typoena/typewriter/docs/adr.md

# Architecture Decision Records

A running log of the load-bearing technical decisions on this project.
Each record states what was considered, what we chose, and what we accept
as a consequence. Status moves from **Proposed** → **Accepted** →
(eventually) **Superseded** when a later ADR replaces it.

Format inspired by Michael Nygard's ADR template, kept short on purpose.

**Related docs:** [`../CONTEXT.md`](../CONTEXT.md) — the glossary and the
principles that constrain [ADR-010]. [`qfd.md`](quality/qfd.md) — the tradeoffs
below, ranked by user-facing weight. [`macroplan.md`](plan/macroplan.md) —
per-version scope.

---

## ADR-001: Language and runtime — Rust on `esp-idf-rs` (std)

**Status:** Accepted — 2026-05-14
**Scope:** Whole project.

### Context

The firmware needs: USB host, Wi-Fi + TLS, SPI peripherals, a SD filesystem,
and a working git implementation that can push over HTTPS. All on an ESP32-S3
with 8 MB PSRAM. We also want the code to stay refactorable as features pile
up across nine downstream releases.

### Options considered

| Option | Pros | Cons |
| --- | --- | --- |
| **C on ESP-IDF (no Arduino)** | Reference platform on the bare native SDK; every peripheral has a driver; smallest binary of the C-family options; no C++ runtime / exceptions / RTTI to reason about. | All memory safety on you; no RAII for resource cleanup; no generics so widget / state code gets repetitive; refactoring at scale is painful. |
| **C++ on ESP-IDF** | Same peripheral coverage as C; RAII, templates, and `std::` containers ease widget / state code; mature in the ESP-IDF examples. | Exception / RTTI story on embedded is messy; ABI / linker surprises; memory safety still on you; binary larger than plain C. |
| **Rust on `esp-idf-rs` (std)**  | First-class Espressif-sponsored Rust support; `std` gives heap / threads / VFS / mbedtls; can use the broader Rust ecosystem (`gitoxide`, `ropey`, `embedded-graphics`). | Larger binary than `no_std`; longer build times; some `unsafe` at FFI seams. |
| **Rust on `esp-hal` (no_std)**  | Smallest binary, most "pure" embedded experience. | No `std` = no off-the-shelf git, no easy TLS, would re-implement a lot of plumbing. |
| **Gleam + Shore on AtomVM** | Beautiful language, the user's stated preference. | BEAM on ESP32 is memory-hungry; no bindings for USB host, e-ink, SD, TLS, git in that ecosystem. Two research projects stacked. |
| **MicroPython / CircuitPython** | Fastest to prototype. | Too slow for responsive editing at the latencies e-ink already imposes; GC pauses would surface as dropped keys. |
| **TinyGo** | Modern, ergonomic. | ESP32-S3 support is thinner than Rust's; smaller ecosystem of embedded crates equivalents. |

### Decision

**Rust on `esp-idf-rs` (std).** It's the sweet spot: keeps the door open to
the entire Rust ecosystem we need (`gitoxide` especially), gets us threads
and TLS without writing them, and has Espressif as an actual upstream.

### Consequences

- Binary will be in the 1–2 MB range — comfortable in 16 MB flash.
- Build times are real (clean build ~5–10 min). Acceptable.
- Cross-compiling toolchain (`espup`) is one more thing to install.
- We will not use `tokio` or async runtimes in v0.1 — see [ADR-006].
- Revisit if `esp-idf-rs` upstream stalls or if `gitoxide` doesn't compile
  cleanly against it (spike 7 was the kill-switch — see [ADR-004]'s Outcome).

See also: [qfd-tradeoffs.md §7](quality/qfd.md#7-tradeoffs-and-their-why-linked-to-adrs) for
the binary-size / build-time costs traded against ecosystem access.

---

## ADR-002: UI strategy — custom widgets on `embedded-graphics`, not Ratatui

**Status:** Accepted — 2026-05-14
**Scope:** Whole project.

### Context

We need a TUI-like editor (header, edit area, status, palettes later). The
output medium is e-ink: pixel framebuffer with **partial-refresh windows**
aligned to panel-internal regions, ~10× slower than an LCD per region.

### Options considered

| Option | Pros | Cons |
| --- | --- | --- |
| **Ratatui** with a custom backend | Mature widget set, well-known API, lots of community examples. | Built for char-grid terminals over ANSI; per-cell diff fights e-ink's region-refresh model; backend would re-rasterise glyphs from cell-diffs; ~200 KB of binary and a leaky abstraction. |
| **Raw `embedded-graphics` only** | Smallest footprint, full control. | Every screen built from primitives; no widget reuse; status line / palette would each be ad-hoc. |
| **LVGL via Rust bindings** | Full GUI toolkit, themable. | Designed for actively-refreshing colour LCDs; e-ink integration is awkward; way more than we need. |
| **Custom thin widget layer on `embedded-graphics`** | Borrow Ratatui's API ideas (`Layout`, `Block`, `Paragraph`) without its rendering model; dirty-rect tracking aligned to e-ink regions; ~500 LoC. | We own and maintain the layer. |

### Decision

**Custom thin widget layer on `embedded-graphics`.** Steal the widget _API
shape_ from Ratatui (because it's a good shape) but render directly to a
pixel framebuffer with our own dirty-rectangle tracking sized to the panel's
refresh regions.

### Consequences

- ~500 LoC of widget/layout code we maintain. Worth it.
- We can tune refresh cadence (partial vs full) at the widget level.
- If we later want to render to a terminal for desktop testing, we add a
  second backend; the widget API stays.

Implementation: the `app::render` engine ([stack](reference/stack.md)).
Owns the two top-ranked functions (H1 latency, H2 region area) in
[qfd-house-1.md §3](quality/qfd-house-1.md#3-house-of-quality--whats--hows).

---

## ADR-003: Display medium — e-ink (GDEY0579T93 panel)

**Status:** Accepted — 2026-05-14
**Scope:** v0.1 through v1.0. 10.3" e-ink upgrade remains on the v1.x table; a non-e-ink swap would supersede this ADR.

### Context

The display has the largest downstream blast radius of any hardware choice.
The _medium_ (e-ink vs. LCD vs. memory LCD vs. OLED) — not the specific
panel — is the real architectural decision: it sets the render strategy
([ADR-002]), the per-keystroke latency floor, the idle-power profile (and
so the v0.8 battery story — [ADR-008]), the UX posture, and the BOM shape.
The specific panel (GDEY0579T93 + DESPI-c579 breakout) is already on hand
and documented here as the _instantiation_, not as a freshly weighed option.

This ADR records the medium choice with eyes open. E-ink has well-known
costs at the typing latencies a writing appliance wants — Astrohaus shipped
the Freewrite Alpha in 2023 on a reflective LCD specifically to address
typing-latency complaints from their original e-ink line. We are accepting
costs the category leader retreated from.

### Options considered

| Option | Refresh / persistence | Pros | Cons |
| --- | --- | --- | --- |
| **E-ink (reflective, image-persistent)** | ~100–300 ms partial / ~700–1000 ms full / persists at 0 W | Paper aesthetic; persists at zero idle power; no backlight (no glare, no eye strain); category convention (Freewrite, reMarkable, Kindle Scribe, Boox); medium enforces writing posture | Slow per-keystroke feedback; ghosting accumulates → periodic full-refresh flash; scroll is the worst-case refresh op (full edit-area redraw); requires waveform / refresh-cadence tuning; Astrohaus retreated from e-ink in Freewrite Alpha (2023) on typing-latency grounds |
| **FSTN graphical LCD (monochrome)** | <16 ms, no refresh quirks | Cheap (~$5–15); trivial render code; snappy scroll | Backlit (always-on power), unreadable indoors without it; no image persistence; calculator / feature-phone aesthetic; writing-grade resolution (≥600 px wide at ≥6") effectively unavailable as a hobbyist part |
| **Sharp Memory LCD (monochrome, reflective)** | ~20 ms, persists at near-0 W | Persists _and_ refreshes fast (best technical combo); sun-readable; ghost-free | Caps around 4.4" before getting rare and expensive; reflective-only feels like a screen, not paper; niche sourcing; lower DPI than e-ink at writing size |
| **TFT / OLED (color, self-lit or backlit)** | <16 ms, persists only at full power | Bright, fast, plentiful | Backlit / self-lit → screen-feel, not paper; OLED burns in static text (status line, header); defeats the writing-tool posture; not seriously a contender |

### Decision

**E-ink as the display medium**, instantiated with the **GDEY0579T93 (5.79",
792×272, SSD1683-class) driven over SPI through the DESPI-c579 breakout** —
which is already on hand. The DESPI-c579 is a passive level-shifter / FPC
adapter, not an active controller — same SPI driver model as any other
e-paper.

The medium is chosen for: paper aesthetic, zero-idle-power persistence
(which makes [ADR-008]'s battery deferral structurally cheap to revisit at
v0.8), the category convention users have a mental model for, and alignment
with the "writing tool, not screen" posture pinned in
[`CONTEXT.md`](../CONTEXT.md). The slow refresh and scroll cost are accepted
as the price of those properties.

### Consequences

- Visible writing column on this panel is ~13 lines. UI must embrace the
  constraint — no multi-pane, no large headers. Region vocabulary:
  [`CONTEXT.md` → screen regions](../CONTEXT.md#screen-regions).
- Framebuffer is ~27 KB; keeps PSRAM free for git pack data — a top-3
  budget item in [qfd-budget.md §6](quality/qfd.md#6-critical-performance-budget).
- Driver: SSD1683-class. If `epd-waveshare` doesn't already cover this
  panel's controller, ~300 LoC of `embedded-hal` SPI driver. Validated in
  [spike 2](../firmware/docs/bring-up-spikes.md).
- **Per-keystroke latency floor ~100–300 ms** (partial refresh). The render
  module must buffer the active line and flush on a short timer, not redraw
  on every keystroke. Owns the top-ranked H1 latency constraint in
  [qfd-house-1.md §3](quality/qfd-house-1.md#3-house-of-quality--whats--hows); strategy lives in
  [ADR-002].
- **Scroll is the worst-case refresh operation** — every scroll is a full
  edit-area redraw, either with a visible flash (full refresh) or
  accumulating ghost trails (partial refresh). The concrete scroll strategy is
  a render concern, not part of this ADR — the scope/trigger vocabulary is in
  [`CONTEXT.md` → refresh cycle](../CONTEXT.md#refresh-cycle).
- **Industry calibration:** Astrohaus shipped Freewrite Alpha (2023) on a
  reflective LCD specifically to fix typing-latency complaints from their
  e-ink line. The latency cost we're accepting is one the commercial leader
  couldn't fully tune away after a decade. Set expectations accordingly —
  do not promise "instant feedback."
- Idle power on e-ink is structurally ~0, which makes the battery sizing
  exercise straightforward — see [ADR-008] and
  [macroplan → v0.10](plan/macroplan.md#v010--power-battery--sleep---).
- 10.3" e-ink upgrade path is preserved by keeping the renderer
  resolution-agnostic. A _non_-e-ink swap (e.g. Sharp Memory LCD) would
  invalidate [ADR-002]'s dirty-rect strategy and force a fresh medium ADR.

---

## ADR-004: Git implementation — `gitoxide` (`gix`)

**Status:** Accepted — 2026-05-14
**Scope:** Whole project, all releases.

### Context

The device must do `add`, `commit`, `push` over the network. Optionally
later: `fetch`, `pull`, `branch`. The library must compile against
`esp-idf-rs` (std, mbedtls available).

### Options considered

| Option | Pros | Cons |
| --- | --- | --- |
| **`libgit2-sys`** (C bindings) | Battle-tested, comprehensive, well-known. | C dependency complicates cross-compile to ESP32-S3; needs mbedtls glue; binary size; less Rust-idiomatic. |
| **`gitoxide` (`gix`)** | Pure Rust, modular crates (we only depend on what we use), idiomatic API, active development. | Smart-HTTP push path is newer than libgit2's; PSRAM allocation patterns less battle-tested on embedded. |
| **Hand-rolled HTTP + pack** | Smallest possible footprint. | Reinventing git internals; pack delta + ref discovery + index updates are not weekend work. |
| **Shell out to `git` binary**  | Trivial. | There is no `git` binary on the ESP32-S3. |

### Decision

**`gitoxide`.** Modular means we pull only `gix-pack`, `gix-protocol`,
`gix-transport`, etc. — not 200 KB of features we don't use. Pure Rust
removes a class of cross-compile pain. The smart-HTTP path is validated in
spike 7 _before_ we commit to integration; if it fails on the device, we
fall back to `libgit2-sys` for v0.1 (documented as the kill-switch in the
risk table).

### Consequences

- We become an early-ish embedded user of `gitoxide`; bugs reported back
  upstream.
- Auth via PAT in an Authorization header — no SSH (see [ADR-005]).
- Performance on PSRAM during pack operations is a watched metric — top-3
  priority in [qfd-budget.md §6](quality/qfd.md#6-critical-performance-budget).

Implementation: the git row of [`stack.md`](reference/stack.md).

### Outcome — Spike 7, 2026-07-05: kill-switch fired

`gix` was ruled out for v0.1 and the fallback taken. gitoxide supports push only
over `file://` and `ssh://` — **not HTTP(S)** — so with HTTPS + PAT fixed by
[ADR-005], the smart-HTTP push path this ADR bet on does not exist yet. We
switched to **`libgit2` (`git2` crate)** and proved `add → commit → push`
(incl. `pull --no-edit` + retry) on desktop
([`spikes/spike7-git-push`](../spikes/spike7-git-push/README.md)). The remaining risk is
now the on-device **libgit2 → xtensa/mbedtls cross-compile** — the very pain
this ADR chose gix to avoid. Full context:
[postmortem](record/postmortems/2026-07-05-spike7-gix-https-push.md). Revisit gix if
its HTTP(S) push lands upstream before v0.1 ships.

---

## ADR-005: Auth — HTTPS + GitHub Personal Access Token

**Status:** Accepted — 2026-05-14
**Scope:** v0.1 through at least v0.9.

### Context

The device must authenticate to GitHub (or other git remotes) to push.
Auth has to be: enterable on a tiny screen-less first-run flow, storable
on-device, and reasonably secure for a personal appliance.

### Options considered

| Option | Pros | Cons |
| --- | --- | --- |
| **HTTPS + PAT** | Trivial to implement; PAT is a string the user pastes during captive-portal setup; works with `gitoxide` smart-HTTP. | Long-lived secret on device; PAT rotation is manual. |
| **HTTPS + OAuth device flow** | No secret typed by hand; user approves on github.com. | Adds an OAuth client app to maintain; token still has to live on device; more first-run UX work. |
| **SSH** | No PAT; per-device deploy keys. | SSH on embedded is heavy (host-key handling, key generation); `gitoxide`'s SSH transport story is less mature than HTTPS; users would have to register the public key on GitHub anyway. |
| **GitHub App with installation token** | Strongest model, rotating credentials. | Massive overhead for a single-user device. |

### Decision

**HTTPS + PAT.** In v0.1 the PAT (and all other config) is compiled into the
firmware binary via build-time env vars — the dev's-only-user model makes the
binary-as-secret-store acceptable. From v0.9 onward, the PAT moves to
encrypted LittleFS with a key derived from the chip's eFuse, so a stolen SD
card alone is not enough.

### Consequences

- The user (= dev, in v0.1) must generate a PAT with `repo` scope and supply
  it as a build-time env var. Provisioning is build-time only.
- PAT is never logged. Validated in code review.
- Rotation in v0.1 = wipe NVS and re-run setup. Proper rotation UI is v0.9
  — see [macroplan → v0.9](plan/macroplan.md#v09--robustness--).
- Revisit if we ever want to support multiple remotes per device with
  different credentials.

---

## ADR-006: Concurrency — `std::thread` + channels, no async runtime

**Status:** Accepted — 2026-05-14
**Scope:** v0.1 through at least v1.0.

### Context

The firmware has several concurrent concerns: USB input, Wi-Fi maintenance,
screen rendering, occasional git operations. None of them are I/O-bound at
the scale where async wins. The number of "tasks" is bounded and small (≤ 8).

### Options considered

| Option | Pros | Cons |
| --- | --- | --- |
| **`std::thread` + channels** | Boring, debuggable, stack traces work, no executor to tune; ESP-IDF FreeRTOS underneath is well-understood. | Each thread costs 8–32 KB stack depending on workload; not zero-cost like async. |
| **`embassy` async** | Trendy, ergonomic, low memory per task. | `esp-idf-rs` and `embassy` don't mix cleanly; adopting embassy means dropping `std` and rewriting against `esp-hal` ([ADR-001] reversed). |
| **`tokio` on `esp-idf-rs`** | Familiar async. | Heavy executor, oversized for ≤ 8 tasks, mbedtls/`gitoxide` integration would need a lot of glue. |
| **Single-threaded event loop** | Smallest memory. | Long-running ops (git push, full refresh) block input. |

### Decision

**`std::thread` + `crossbeam-channel`.** Five tasks (`usb`, `wifi`, `ui`,
`render`, `git`). Editor state behind a single `Mutex`. No `await`, no
runtime to tune, no colour-of-functions problem.

### Consequences

- Tens of KB of stack space across the task stacks — the measured sum and its
  ceiling are the H11 row of
  [qfd §6](quality/qfd.md#6-critical-performance-budget). Comfortable in the
  ESP32-S3's 512 KB internal SRAM.
- Refresh / git / Wi-Fi each get their own thread, so a slow push doesn't
  freeze typing.
- If task count balloons past ~10 (unlikely), revisit.

---

## ADR-007: Storage split — FAT-on-SD for working copy, LittleFS-on-flash for config

**Status:** Accepted — 2026-05-14
**Scope:** Whole project.

### Context

Two storage needs: a large, removable, growable area for the git working
copy and notes; and a small, durable, never-removed area for device config
(Wi-Fi credentials, PAT, remote URL).

### Options considered

| Option | Pros | Cons |
| --- | --- | --- |
| **SD (FAT) for working copy + LittleFS (internal) for config** | Plays to each medium's strengths; user can pop the SD to read on desktop; config can't be lost by yanking the card. | Two filesystems to manage. |
| **All on SD** | One filesystem. | Config disappears if SD is removed; PAT on FAT is harder to protect than on encrypted NVS. |
| **All in internal flash** | Single medium; encrypted. | 16 MB flash limits notes growth; no desktop-side access; SD slot becomes pointless. |
| **SPIFFS for everything** | Single FS, well-known on ESP32. | SPIFFS isn't great with large files; no removability. |

### Decision

**FAT on SD for `/sd/repo/` and `/sd/local/`. LittleFS on internal flash
for `/nvs/config.toml`.** PAT inside config is encrypted with an eFuse-
derived key.

### Consequences

- User can plug the SD into a laptop and read/edit files there.
  Discouraged but possible.
- Config survives SD reformatting.
- Power-loss safety on FAT is weaker than LittleFS — we mitigate with
  atomic-rename writes (`firmware::infrastructure::storage_sd`).
- **FatFS caveat (Spike 3, verified 2026-07-11):** FatFS's `f_rename` returns
  `FR_EXIST` on an existing destination — it does **not** replace like POSIX
  `rename(2)`. So the atomic save must `f_unlink` the target before renaming the
  `*.tmp` over it, and pair that with **boot recovery** of a lingering `*.tmp`.
  Recovery is _not_ simply "promote the tmp": a crash _during_ the tmp write
  leaves a partial tmp, so the choice depends on whether the target survived —
  - **tmp + target both present** → the crash could have been mid-write, so the
    tmp is untrustworthy. Keep the committed target, discard the tmp (this is the
    documented "you get the previous version" behaviour).
  - **tmp only, target absent** → the target was already unlinked, so the tmp is
    the newest complete, fsync'd copy and the only one left. Promote it.

  Implemented in `firmware::persistence::Storage::{save,recover}`. See the
  [Spike 3 postmortem](record/postmortems/2026-07-05-spike3-sd-cmd59.md#resolution-2026-07-11).

- **SD-card compatibility:** use a genuine card, ideally **≤32 GB (SDHC/FAT32)**.
  Large or counterfeit SDXC cards may reject `CMD59` (SPI-mode CRC) and fail to
  mount; we keep CRC required rather than run the user's writing over an
  unchecked bus. The device reports a swap-the-card message instead of a hex
  code.

### Outcome — the config half was never built

The working-copy half shipped as decided: FAT on SD at `/sd/repo` + `/sd/local`.
The config half did not. There is no LittleFS partition and no
`/nvs/config.toml`; device config lives in **`/sd/typoena.conf`**, plain text on
the same FAT card, written by either onboarding path (installer or wizard) and
read at boot through the `conf` crate. So config does _not_ survive a card
swap, and the eFuse-encrypted-at-rest endgame this ADR assumed is unbuilt —
tracked as the open [ADR-011]. A future ADR should supersede this one if the
split is ever revisited.

---

## ADR-008: MVP power — wall-powered, battery deferred to v0.8

**Status:** Accepted — 2026-05-14
**Scope:** v0.1 only. Revisited in ADR-future at v0.8.

### Context

"DIY typewriter" suggests portability, which suggests battery. But battery
adds: charging circuit, BMS, thermal margin, soft power switch, lid-close
detection, sleep states. Each of those has its own bring-up cost.

### Options considered

- **USB-C wall power, no battery.** Simple, safe, lets us measure real
  draw before sizing a cell.
- **18650 + IP5306 from day one.** Pretty close to a known-good pattern;
  IP5306 handles charge + 5 V boost.
- **LiPo + dedicated charger IC + buck/boost.** More control, more parts.

### Decision

**Wall power only for v0.1.** Battery is its own phase (v0.8) once the
power profile of "boot + type + idle + push" is measured on real hardware.
Sizing a battery before measuring is guessing.

### Consequences

- v0.1 device is tethered. Not the final aesthetic, but the right MVP.
- We can decide cell capacity from real numbers in v0.8, not specs sheets.
- Lid-close detection / deep sleep slips to v0.8 with the battery — see
  [macroplan → v0.10](plan/macroplan.md#v010--power-battery--sleep---).

---

## ADR-009: Keyboard transport — USB host (TinyUSB)

**Status:** Accepted — 2026-05-14
**Scope:** v0.1 through at least v1.0.

### Context

The Nuphy keyboard speaks both wired USB-C (HID) and Bluetooth LE (HID).
The ESP32-S3 has USB OTG (host capable) and BLE 5. Either transport works.

### Options considered

| Option | Pros | Cons |
| --- | --- | --- |
| **USB host (TinyUSB)** | Keyboard draws no battery of its own; ESP32-S3 powers it through the host port; standard boot-protocol HID is well-supported; no radio contention with Wi-Fi during push. | One more USB connector on the enclosure; cable between device and keyboard (or shared chassis). |
| **BLE-HID** | No cable; keyboard can be slightly remote from the device. | Keyboard has its own battery to manage; BLE shares the 2.4 GHz radio with Wi-Fi, so a `Ctrl-G` push contends with input; pairing UX is more first-run work. |
| **UART receiver (custom keyboard firmware)** | Lowest latency, simplest stack. | Requires reflashing the Nuphy or building a passthrough; not viable as a product choice. |

### Decision

**USB host (TinyUSB) for v0.1.** BLE-HID is kept as a documented fallback
if TinyUSB host turns out unstable
([spike 4](../firmware/docs/bring-up-spikes.md) is the gate).

### Consequences

- Enclosure design must include a USB-A or USB-C port for the keyboard.
- The Nuphy's own battery is irrelevant when wired — saves the user a
  charging surface.
- Wi-Fi and keyboard input do not contend for radio time.
- If we ever want a fully wireless build, we revisit with a BLE-HID ADR.

---

## ADR-010: Push UX — atomic `Ctrl-G`, auto-timestamp commit message, no user prompt

**Status:** Accepted — 2026-05-14
**Scope:** Whole project, all releases.

### Context

The device needs an action that ships writing to the git remote. Most
git-using tools expose `commit` and `push` as distinct user gestures, often
with a commit-message prompt. The device's actual user (= the author of this
firmware) already uses the [`gct` shell alias](../CONTEXT.md#user-facing-actions)
for their own writing: `git add . && git commit -m "<timestamp>" && git push`,
with a `git pull --no-edit` fallback when the push fails non-fast-forward.
`gct` is the established workflow; the typewriter mirrors it.

### Options considered

| Option | Pros | Cons |
| --- | --- | --- |
| **Three separate gestures** (save / commit / push) | Maximally git-native; user has fine control. | Three keys to remember, three failure modes to surface, three concepts in the user's head. Wrong shape for an appliance whose job is to remove ceremony. |
| **One gesture, prompt for message** (`Ctrl-G` → modal asking for message → commit → push) | Conventional "push" pattern; each commit is named. | A modal prompt on e-ink is hostile (latency, full refresh); the user's actual workflow (`gct`) explicitly avoids authoring messages; messages would be noise (`"updated notes"` × 1000). |
| **One gesture, auto-timestamp message** (`Ctrl-G` mirrors `gct`) | Matches the user's real workflow; one key, one outcome; no prompts, no modes, no decisions in the writing path. | Commit history is timestamp-noise (useless for code archaeology); a future reader will wonder where the commit messages went; locks in a UX assumption that's hard to undo without breaking muscle memory. |

### Decision

**One gesture, auto-timestamp message, atomic from the user's view.** `Ctrl-G`
runs the full `gct` sequence (stage all → short-circuit if nothing staged →
commit with ISO-8601 timestamp → push → on push failure, `pull --no-edit` then
retry). Failure surfaces as a single retry-able outcome in the status line.

### Consequences

- The user's vocabulary collapses to **Save** and **Push**;
  [`CONTEXT.md`](../CONTEXT.md#user-facing-actions) pins this — _commit_ is
  not a user-facing term.
- Commit history is a stream of timestamps. The device is a writing tool, not
  a code repository — the history is here for recoverability, not narrative.
- The pull-merge-retry path means the device may author merge commits on the
  user's behalf, with git's default merge message. Acceptable: the user
  doesn't read commit history from the device anyway.
- The previously-planned "commit message prompt" item in v0.7 has been
  removed from the roadmap.
- Reversing this later (introducing message prompts) would change the
  semantics of `Ctrl-G` and break the user's muscle memory. Hard-to-reverse
  by design.

### Outcome — as shipped (recorded 2026-07-16)

The user contract held — one deliberate action, auto-message, atomic outcome,
no prompt — but three mechanics drifted from the letter of this ADR as the
implementation matured:

- **The trigger is the `:gs` ex command, not `Ctrl-G`.** It pairs with `:gl`
  (pull), Normal mode binds the bare `gs`, and the palette exposes it as
  `> push`. The keymap has no `Ctrl-G` binding at all. The muscle-memory
  lock-in argument transferred intact to the ex command.
- **The commit message is `Typoena push — unix <epoch>`**, not the
  ISO-8601 string this ADR specified. Same
  contract (device-authored timestamp noise, zero prompts), different
  format; nothing downstream parses it.
- **Rejected pushes replay, they don't merge.** The decision text said
  "`pull --no-edit` then retry" (merge commits); the shipped path fetches
  and re-splices the device's commit onto the remote tip — **no merge
  commits**, so the "device may author merge commits" consequence above
  never materialised. [`CONTEXT.md`](../CONTEXT.md#user-facing-actions)
  documents the replay model.

Heading and anchor kept for link stability.

---

## ADR-011: Credential provisioning — how the PAT reaches the device and is protected at rest

**Status:** Proposed / **Open** — 2026-07-07 (deferred beyond v0.1)
**Scope:** Gates the first distribution to any non-dev user.

### Context

[ADR-005](#adr-005-auth--https--github-personal-access-token) decided the auth
model (HTTPS + PAT) and sketched an endgame ("from v0.9 the PAT moves to
encrypted storage with an eFuse-derived key"), but left the _mechanics_ open:
**how does a token get onto a device, and how is it protected once there?**

Spike 7 made this concrete. The PAT is currently **baked into the firmware image
at build time** (`build.rs` → `env!()` → a `const` in the `.bin`) — ADR-005's
deliberate v0.1 shortcut. On a real device that means:

- the token sits in **plaintext in flash** — anyone with physical access can
  `esptool read_flash` and extract a working GitHub PAT (push/pull as the user);
- it is the **same token on every unit** built from that image — no per-device
  revocation;
- **rotation requires a reflash**.

This is fine for the dev's own bench unit (it's their token, their device) and is
why the [Spike 7 postmortem](record/postmortems/2026-07-05-spike7-gix-https-push.md)
lists it as the _last standing shortcut_. It is not fine for a unit in anyone
else's hands. Resolving it needs a **provisioning path**, which the v0.1 design
(build-time only, no provisioning module) deliberately omits.

### Options considered

| Option | Pros | Cons |
| --- | --- | --- |
| **Build-time bake** (current, ADR-005 v0.1) | Zero UX; nothing to build. | Plaintext in flash; same token per unit; reflash to rotate. **Dev-bench only.** |
| **On-device paste → NVS (plaintext)** | No reflash; per-device token. | Still plaintext at rest; needs a first-run entry UI (captive portal / keyboard). |
| **On-device paste → NVS encrypted (eFuse key)** | ADR-005's stated target; a flash dump alone doesn't yield the token; per-device + rotatable. | Needs NVS encryption + eFuse key derivation + first-run UI — the whole provisioning module. |
| **USB provisioning tool** (host writes NVS over serial) | No on-device text entry; scriptable at assembly. | Needs a host-side tool; token still needs at-rest protection (combine with encryption). |
| **Per-device fine-grained PAT** (orthogonal) | Least blast radius; per-device revoke; repo-scoped. | User mints one PAT per device; pairs with any storage option above. |
| **GitHub App installation token** | Strongest, rotating creds. | Heavy for a single-user appliance — rejected in ADR-005 for overhead. |

### Decision

**Open — deferred.** v0.1 stays on the build-time bake (dev-bench only). Before
shipping to any non-dev user, pick a provisioning mechanism — the likely shape is
**on-device paste → eFuse-encrypted NVS** (ADR-005's target) **+ a per-device
fine-grained PAT** to bound the blast radius. That requires the provisioning
module currently deferred, NVS encryption, and eFuse key derivation, and ties
into [ADR-007](#adr-007-storage-split--fat-on-sd-for-working-copy-littlefs-on-flash-for-config)
(where config lives).

### Consequences

- **Blocks nothing in v0.1** — the bench unit runs on the baked PAT.
- **Gates first non-dev distribution** — this ADR must flip to Accepted (with a
  chosen mechanism) before a unit leaves the dev's hands.
- Whatever is chosen, the token must never be logged or written into the working
  copy — already enforced in the git module (PAT lives only in libgit2's
  credential callback).
- Rotation UX and the first-run flow are the real work here, not the crypto.

### Outcome — half of it shipped, the crypto half did not

The delivery mechanism is settled and built: the token reaches the device
through the **GitHub App device flow**, run by either the on-device
[wizard](plan/v0.9-onboarding-wizard.md) or the macOS
[installer](../installer/DESIGN.md), and both write it to `/sd/typoena.conf`.
Nothing is baked into the image any more, and a token is per-device and
revocable — which was the blast-radius half of this ADR.

**At rest is still open.** The token sits in plaintext on a FAT card that pops
out; physical custody of the card is the only control, and the eFuse-encrypted
storage this ADR names stays designed-but-unbuilt (see [ADR-007]'s Outcome —
the LittleFS partition it would live on was never created). Status stays
**Open** on that ground alone; the trigger to resolve it is in
[qfd §7](quality/qfd.md#conflicts-left-explicitly-unresolved-by-v01).

---

## ADR-012: SD on its own SPI3 host (not shared with the EPD on SPI2)

**Status:** Accepted — 2026-07-11
**Scope:** v0.1 hardware; whole project.

### Context

The EPD (SSD1683) and the SD card both want SPI. The v0.1 plan (the boot
sequence and the storage context of
[ADR-007](#adr-007-storage-split--fat-on-sd-for-working-copy-littlefs-on-flash-for-config))
assumed **one shared SPI2 bus** with a per-device chip-select. Spike 3 (verified
2026-07-11, [postmortem](record/postmortems/2026-07-05-spike3-sd-cmd59.md)) proved the
SD works on the SPI2 wiring, but surfaced the integration blocker: the EPD driver
uses esp-idf-hal's `SpiBusDriver`, whose constructor takes an **exclusive
`spi_device_acquire_bus(BLOCK)` and holds it for the driver's whole lifetime**
(it must keep CS asserted across a cmd→data sequence while toggling DC). While
held, no other device on that host can transact — so an SD on SPI2 is locked out
for as long as the panel driver is alive. Compounding it, persistence/git runs on
a **dedicated thread** (Spike 7) while the EPD refreshes on the main task, so SD
and EPD access are genuinely concurrent.

### Options considered

| Option | Pros | Cons |
| --- | --- | --- |
| **Shared SPI2, arbitrate** | One bus; ~2 fewer GPIOs. | Rewrite the proven EPD SPI layer to per-transaction device drivers; add a cross-thread mutex around all SPI2 access; residual "corruption on save during render" risk on the highest-value path. |
| **SD on its own SPI3** | EPD code untouched; no arbitration/mutex; each bus at its own clock; matches the risk-table fallback exactly. | ~2 extra GPIOs + traces. |

### Decision

**SD gets its own SPI3 host.** The EPD keeps SPI2 and its exclusive-lock model,
unchanged. This is the mitigation the technical-doc risk table already names
("move SD to a separate SPI peripheral — ESP32-S3 has two"). SPI3 is free (SPI0/1
are flash + PSRAM; nothing else uses SPI3).

Pins — **SD on SPI3:** SCK 14, MOSI 15, MISO 13, CS 10 (MISO/CS unchanged from
the spike; only SCK/MOSI move off the EPD-shared 12/11). **EPD stays on SPI2:**
SCK 12, MOSI 11, CS 7, DC 6, RST 5, BUSY 4.

### Consequences

- No shared-bus arbitration or mutex — the git thread's SD I/O never contends
  with an EPD refresh. Removes the "corruption on save during render" risk for
  the device's first value (not losing the user's writing).
- Each bus runs at its own clock (EPD ~4 MHz on jumpers; SD 10 MHz+).
- Costs ~2 extra GPIOs + traces; the pin budget has room (avoids flash 26–32,
  octal PSRAM 33–37, strapping 0/3/45/46, USB 19/20, RGB 38/48, EPD 4–7/11/12).
- Supersedes the "shared SPI2, different CS" assumption in the boot sequence and
  ADR-007's storage context; the `sd_fat` spike is rewired to SPI3 and its
  EPD-CS-deselect step (only meaningful on a shared bus) is removed.
- The `SpiBusDriver`-holds-the-lock mechanism was read from the constructor, not
  re-verified on silicon; it doesn't affect this decision (SPI3 sidesteps it),
  but is the first thing to confirm if a shared bus is ever revisited.

---

## ADR-013: Firmware architecture — adopt the hexagonal ports refactor over the flat crate

**Status:** Accepted — 2026-07-18 (on-device smoke test passed — see Outcome)
**Scope:** Whole firmware crate + the host-crate workspace. Retires the flat `firmware/` module layout.

### Context

`refactor/whole-repo` (checked out as the `../typewriter-refactor` **worktree**) is
not a second codebase — it is this same repo, diverged from `main` by exactly **one
commit each way** from merge-base `0c9a106`:

- `main` is ahead by `b93aa90` (`feat(conf): complete a bare repo name with the GitHub user`).
- `refactor/whole-repo` is ahead by five commits that rework the firmware onto a
  **ports-and-adapters (hexagonal)** shape, modelled on the C `../typing-machine`
  reference:
  - `hal/` — pure `Screen` / `Keyboard` trait contracts, no esp-idf types.
  - `app/` — a host-testable application layer: the `Panel` render engine (generic
    over `hal::Screen`), the application ports (`Storage`, `SyncService`, `Clock`,
    `System`, `FileIndex`), and a `Runtime` that lifts the ~300-line editor loop out
    of `main.rs`.
  - `firmware/` regrouped into `drivers/` (esp-idf adapters) + `infrastructure/`
    (SD storage, git sync, file index, wizard I/O) tiers; `main.rs` becomes a
    boot/composition root.
  - a root Cargo **workspace** over the seven pure crates — one lock, one `target/`,
    one `cargo test` for all of them (previously each crate carried its own lock and
    was tested individually).

So the real question is not "which folder is best" but **"do we land this refactor
on `main`, or abandon the branch and keep growing the flat crate?"** — decided here
on measured evidence, not preference.

### Criteria

Ranked by weight for this project — a solo, on-device appliance where the device
loop is the slow, expensive feedback path:

1. **Off-device testability** — can run-loop logic be proven on the host, not the
   bench? (Top weight: every on-device cycle costs a flash + a manual smoke.)
2. **Separation of concerns / maintainability** — is the layering visible and the
   god-file broken up?
3. **Behaviour equivalence & feature parity** — same shipped behaviour, no lost
   features.
4. **On-device verification** — proven on the ESP32-S3, per project norm.
5. **Merge / divergence cost** — how expensive to land, and does waiting make it
   worse?
6. **Complexity cost** — does the added indirection earn its keep, or is it ceremony?
7. **Build / CI ergonomics** — one `cargo test` and one lock, or per-crate.

### Options considered

| Option | Pros | Cons |
| --- | --- | --- |
| **A. Adopt the refactor** (merge `refactor/whole-repo`, rebase `b93aa90` over it) | Run-loop becomes host-testable (**+29 `app` tests**, within **358 green** workspace tests); `main.rs` **924 → 368** lines; layering visible in the tree; one-command workspace test; indirection is disciplined — only genuine seams abstracted, Wi-Fi/git fusion deliberately left concrete | Not yet flashed on device — compile+link verified only; one more layer (ports) to learn; a little port ceremony |
| **B. Keep `main` flat**, abandon the branch | Zero merge work; fewest moving parts; every line already device-proven | Run-loop stays locked in a 924-line `main.rs`, untestable off-device; the god-file keeps growing over nine more releases; discards a clean, working refactor |
| **C. Cherry-pick parts** (workspace + tests, skip the `hal`/`app` ports) | Some test benefit without the layering | The tests **are** what the ports enable — you cannot host-test the loop without lifting it off the concrete hardware types; splitting the branch is more work than merging it |

### Decision

**Option A — adopt the refactor**, gated on a single on-device smoke test before the
merge lands.

It wins decisively on the top three criteria and loses on none where `main` isn't
trivially recoverable:

- **Testability (the whole point):** the `Runtime` is driven through ports with
  in-memory doubles, so save / delete / push-dispatch / pull-dispatch /
  "a pull that moves the tree reloads the active buffer and rewalks" / every
  snackbar variant are now **host** tests (`app/src/runtime/tests.rs`). That logic
  used to live in `main.rs` and could only be exercised by flashing.
- **Maintainability:** `main.rs` drops **924 → 368** lines and becomes a composition
  root; the `drivers/` + `infrastructure/` split makes the layering legible.
- **Discipline:** the design abstracts only real seams and explicitly *refuses* to
  port the Wi-Fi radio (inseparably fused with git sync) — the indirection earns its
  keep rather than being architecture-astronaut ceremony.
- **Merge cost is at its global minimum right now:** one commit each way. Every day
  `main` evolves on the flat structure widens the rebase. This is the cheapest this
  decision will ever be.

### Consequences

- **Gate cleared — on-device smoke test passed (2026-07-18).** Green on 358 host
  tests, the full `firmware` binary builds for xtensa, and the whole run-loop was
  exercised on the bench ESP32-S3 (see Outcome below). The one residual risk —
  runtime behaviour on silicon — is now observed, not inferred.
- **After merge:** rebase `b93aa90` onto the refactor tip (trivial — it touches
  `conf`, untouched by the refactor), then `git worktree remove ../typewriter-refactor`
  and delete the `refactor/whole-repo` branch. The flat layout is retired:
  `firmware/src/{epd,usb_kbd,net,git_sync,adapters}.rs` no longer exist as such.
- **The two esp-idf binaries (`firmware`, `installer`) stay outside the workspace by
  design** — different target triple / release cadence; they consume `hal`/`app` by
  path across the boundary. Correct, not a gap.
- **Reversibility:** the pre-refactor state stays in history at `b93aa90`; backing out
  later is a `git revert` of the merge, not a rewrite. This is why the framing is
  "merge or not," never "delete the loser."

### Outcome — on-device verification (2026-07-18)

Flashed to the bench ESP32-S3 (release, `--features git`, build `g56f8ef2`) and ran
the full smoke test end to end. Every port the refactor introduced fired on silicon,
matching its host double:

- **Boot + render:** cursor ready 3239 ms; the extracted `app::render` engine drives
  the panel — windowed per-keystroke refresh in Insert (~491 ms), full-area on mode
  change (~525 ms).
- **`Storage` (write):** opened `_inbox/2026-07-09.md` (695 B), edited in Insert, `:w`
  saved **703 B** to the card.
- **`SyncService` (push):** `:gp` brought Wi-Fi up, committed `8470d7ac`, and the
  **push was accepted by the remote** (push 28.8 s).
- **`SyncService` (pull) + `FileIndex`:** `:gl` fast-forwarded `main`
  `8470d7ac → bcff040e` (2 files) and triggered the post-pull rewalk — the on-device
  counterpart of the `pull_that_moves_the_tree_reloads_active_and_rewalks` host test.
- **`Clock`:** SNTP synced (`unix 1784387806`). An earlier run also confirmed the
  `SyncService` **RefusedDirty** gate (`:gl refused — dirty journal non-empty`).

Only the `System` port (`:reboot` / `prepare_setup`) was not re-exercised — the
lowest-risk seam (a marker write + `esp_restart`, and its save leg is the now-proven
`Storage` path). Status flipped to **Accepted**; the refactor is clear to merge.

---

## How to add a new ADR

1. Append a new `## ADR-NNN: <title>` section to this file.
2. Status starts as **Proposed**, with today's date.
3. Once merged + agreed, flip to **Accepted**.
4. When superseded, leave the old ADR in place and add **Superseded by
   ADR-MMM** to its status line. Never delete.
5. Cross-reference from the relevant section of the README or design docs
   if the decision is load-bearing for code review.

[ADR-001]: #adr-001-language-and-runtime--rust-on-esp-idf-rs-std
[ADR-002]: #adr-002-ui-strategy--custom-widgets-on-embedded-graphics-not-ratatui
[ADR-003]: #adr-003-display-medium--e-ink-gdey0579t93-panel
[ADR-004]: #adr-004-git-implementation--gitoxide-gix
[ADR-005]: #adr-005-auth--https--github-personal-access-token
[ADR-006]: #adr-006-concurrency--stdthread--channels-no-async-runtime
[ADR-007]: #adr-007-storage-split--fat-on-sd-for-working-copy-littlefs-on-flash-for-config
[ADR-008]: #adr-008-mvp-power--wall-powered-battery-deferred-to-v08
[ADR-009]: #adr-009-keyboard-transport--usb-host-tinyusb
[ADR-010]: #adr-010-push-ux--atomic-ctrl-g-auto-timestamp-commit-message-no-user-prompt
[ADR-011]: #adr-011-credential-provisioning--how-the-pat-reaches-the-device-and-is-protected-at-rest
[ADR-012]: #adr-012-sd-on-its-own-spi3-host-not-shared-with-the-epd-on-spi2
[ADR-013]: #adr-013-firmware-architecture--adopt-the-hexagonal-ports-refactor-over-the-flat-crate
