typoena/typewriter/docs/plan/v0.9-onboarding-wizard.md

# v0.9 — On-device onboarding wizard (first boot + `:setup`)

> Part of the [Typoena macro plan](macroplan.md) — this doc expands the
> "on-device provisioning + settings screen" item of
> [v0.9-robustness.md](macroplan.md#v09--robustness--). Requirements and targets:
> [qfd.md](../quality/qfd.md). Load-bearing decisions: [adr.md](../adr.md).

**Status:** built and verified on hardware, slices 0 through 5c. First boot
(Wi-Fi scan-pick, GitHub device-flow QR, repo pick, shallow clone) and
`:setup`'s three sub-flows (Wi-Fi / re-auth, factory reset, repo switch) all
run on the panel. The conf key for the token is `TW_TOKEN`; legacy `TW_PAT`
still parses.

**Deferred:** a **SoftAP companion webapp** for a phone-driven Wi-Fi hand-off,
chosen over BLE because Web Bluetooth is unsupported in iOS browsers. It
reverses the no-SoftAP non-goal below when it lands, and it only moves typing
to the phone — no browser API exposes a stored Wi-Fi password. The on-device
keyboard path stays as the no-phone fallback.

## Why

The [installer](../../installer/DESIGN.md) provisions an SD card from a Mac. The
wizard is the **zero-computer onboarding path**: a device fresh from the box,
powered on with a blank card, configures itself with only its own keyboard, its
panel, and the user's phone. It is a **peer** of the installer, not a
companion — two paths to the same configured card. It covers the no-Mac and
no-computer-at-all users, and it lets typoena.dev lead with "just power it on."

## Trigger

**Unconfigured = no `/sd/typoena.conf`** — not "card empty": fresh cards carry
junk (`System Volume Information`, `.Spotlight-V100`, …). The check lives in
`boot_storage` (`firmware/src/main.rs`), which already halts on no-SD and
no-repo; an unconfigured card branches into the wizard instead of
`boot_halt`. A configured card boots the editor exactly as today.

## Prerequisite — runtime config

The card, not the image, is what configures a device — which is what makes an
*installer*-provisioned card work for someone who is not the firmware author:

- A shared **`conf` crate** (host-buildable, no esp deps) owns the schema:
  the seven `TW_*` keys, required-ness, `KEY=value` parse/render, and
  `expand_remote_url`. The installer still carries its own copy in
  `installer/src/config.rs` and should consume the crate instead — one source
  of truth, not yet done.
- At boot the firmware parses `/sd/typoena.conf` into a `Conf` and threads it
  to the git thread; the `env!("TW_*")` consts baked by `build.rs` are the
  **fallback** for values the card doesn't carry, so dev builds keep working.
- Precedence: **card overrides baked**. A field empty in both is caught by the
  existing runtime `bail!` guards in `push_cycle`/`pull_cycle` (snackbar on
  first `:gs`/`:gl`), or by the wizard itself.

## The wizard

A step sequence rendered directly into a `display::Frame` (the
`show_message`/`boot_halt` pattern — no editor loop), consuming `keymap::Key`
from `usb_kbd::next_key()`. The step/field state machine lives in a
host-testable crate (`wizard/`, deps `keymap` + `display` + `conf`), with the
palette's `NewFile` input step as the editing model (Enter commits,
Backspace-past-start goes back). Every completed step persists atomically
(unlink + `*.tmp` + rename — FAT `f_rename` won't overwrite), so a power-pull
resumes at the right step, never in a half-configured boot.

1. **Welcome + Wi-Fi.** The device scans on entry and shows nearby networks
   as a **filterable pick list** (deduped, strongest-first) — the SSID is
   *selected*, not typed. Esc drops to manual entry for a hidden/missed
   network. Only the **password is typed**, on the device keyboard, and it is
   **shown by default** (Tab hides it) so a long random key isn't entered
   blind — justified by the device's own security model (secrets sit in
   cleartext on the card; physical custody is the control). Join is tested
   immediately (`net.rs::connect_wifi`, bounded retry) with a clear failure →
   re-edit loop. **Decision (revisited): no SoftAP/captive portal *in the
   on-device wizard*** — an embedded HTTP server + captive DNS + web UI is a
   whole firmware subsystem, and the scan-pick + reveal cover the keyboard
   step well. A SoftAP *companion webapp* is a separate, deferred path (see
   the status note) for users who'd rather not type the password on the
   device at all. Note: the modem currently moves into the git thread at
   boot; the wizard runs **before** that thread spawns, so it owns the modem
   during setup (scan + join) and releases it to the normal boot path when
   done. The radio is built once, started/stopped for the scan, then kept up
   from the join onward.
2. **Sign in with GitHub — the QR step.** The device runs the GitHub App
   device flow itself (client_id `Iv23liwgnE86ITDpBdnn`, same app as the
   installer's ^G): POST `login/device/code`, render the `verification_uri`
   as a **QR code on the e-paper** with the 8-char `user_code` printed under
   it, poll `login/oauth/access_token` at the server's interval, store the
   token. The phone is needed exactly once — scan, tap approve, done; the
   user never types a token. HTTPS via `EspHttpConnection` (the Spike 6
   client, promoted into the firmware proper with POST support);
   SNTP/trust-store setup reuses the `ensure_online` pieces. QR modules drawn
   as filled rects into the `Frame` (a QR generator is net-new — small
   pure-Rust encoder, no_std-friendly).
3. **Pick the repo.** GET the installation's repo list from the API, render
   as a keyboard-navigable list; identity (author name/email) prefilled from
   `/user`. Creating a repo is out of scope on-device — the GitHub App's
   installation page on the phone covers "grant a new repo" if needed.
4. **Clone — with a size gate.** The device clone is **shallow fetch
   (depth 1) + `apply_tree_diff(empty → tip)`** — `git init` at `/sd/repo`,
   set origin, fetch with `FetchOptions::depth(1)` (git2 0.20 / libgit2
   1.9.4), then the v0.7 O(changed) tree apply writes the working copy. The
   result is a **single pack** (the pack-not-loose state FAT wants) and media
   is skipped at checkout (`is_media_path`), exactly like `:gl`.
   **But libgit2 has no partial clone** (no blob filters), so tip media *is*
   downloaded even though it's never written. Hence the gate: before
   fetching, read `repo.size` (KB) from the API; **over ~30 MB the wizard
   refuses** with the honest message — *"this repo is too large to set up
   from the device — pick or create a smaller one, or seed the card from a
   computer once (typoena.dev)."* No workaround is pretended. (Future lever
   if ever needed: a pack-trimming proxy on typoena.dev infra — parked, real
   infra + token-trust cost.) Under the gate: progress on the panel
   (download, then per-file apply — ~1100 files is minutes on FAT-over-SPI,
   fine one-time with a progress line). Then seed `.typoena.toml`, the
   snippet catalog, and `/sd/local` if absent — the defaults move **into the
   firmware** (canonical copy; the installer should bundle from the same
   source so the two paths can't drift).
5. **Done.** Write the final conf, fall through to the normal boot path
   (note load, walk, git thread, editor).

## `:setup` — reset is the same wizard, prefilled

A second entry mode, not separate machinery: the `:setup` ex command (one arm
in `execute_command`, plus a `>` palette entry) reopens the wizard **prefilled
from the current conf** — the device-side derive ladder. Change Wi-Fi, re-auth,
or switch repos by skipping to the step you care about.

- **Config is rewritten only when a completed step changed something**
  (tmp + rename). Opening `:setup` and backing out is harmless — no
  delete-config-and-reboot.
- **Same repo re-chosen** → `/sd/repo` untouched, no re-clone, dirty journal
  survives. The no-op keys off the repo actually on disk (`repo_on_disk`), not
  the conf's remote — so a re-pick after a failed switch (which deleted the old
  tree) is treated as a fresh switch, never a no-op onto a repo that isn't there.
- **Different repo** (slice 5c, BUILT 2026-07-16) → the **dirty guard is
  mandatory**: a non-empty `.typoena-dirty` journal refuses with "push first
  (`:gs`)" and the switch never starts. A picked repo is confirmed with a plain
  Enter/Esc (not the typed word factory reset needs — the dirty guard already
  guarantees nothing unpushed is lost). On confirm the `DeleteRepo` effect
  removes `/sd/repo` on the main task (via `Storage::wipe_repo` → the same
  FAT-safe `remove_tree`) **before** the new conf is written, so a power-pull
  once the tree is gone re-enters the wizard rather than booting a repo that
  disagrees with the conf; then the shared clone worker fetches the new tip.
  Tree delete + clone over FAT is minutes at ~1100 files — the `Cloning` screen
  streams progress ("removing the old repo", then the clone's own lines). If the
  clone fails the old tree is already gone, so `Done` is refused until a clone
  completes (finishing would boot a card with no working copy); the pick list's
  Esc returns to the menu. **Deferred to slice 5d if ever needed:** a
  content-aware boot check — the boot gate keys off `repo_present` (dir exists),
  so the narrow window *during* the delete (dir half-emptied, conf still old) or
  *during* the clone can still boot a broken repo on a power-pull. This is the
  same window first-boot's clone already tolerates for a one-time step; it
  self-heals on the next power cycle (missing/partial repo → wizard resume).
- **Factory wipe** (back to blank-card state) is a final confirmed option
  *inside* the wizard, not its own command — **built in slice 5b**. Selecting
  *Factory reset* opens a confirmation that requires typing `erase` (spelled
  out on the panel; case-insensitive). It erases **everything**: `/sd/repo`,
  `/sd/local` (unpushed scratch — no remote copy, so the confirm names it),
  `typoena.conf`, the `/sd/ca.pem` trust store, and the `.typoena-*` markers,
  then reboots into first boot. A non-empty dirty journal doesn't block the
  wipe (it's a wipe) but adds a louder warning line — "unpushed notes will
  be LOST — `:gs` first". Delete order is repo → local → conf, so a power-pull
  mid-wipe still reads as unconfigured at boot and re-enters the wizard rather
  than booting a half-erased card. **Deliberate deviation from "or a stranded
  commit":** the guard reads only the `.typoena-dirty` journal, not libgit2
  stranded-commit state — a failed `:gs` returns its paths to the journal, so
  a stranded commit already shows as a non-empty journal; the journal-empty-
  but-stranded case isn't reachable through the normal flow, and opening the
  repo with libgit2 on the wizard's main stack to detect it isn't worth the
  cost. The recursive delete is a FAT-safe both-tables `remove_tree` in
  `persistence.rs` (std's `remove_dir_all` trusts the wrong DT constants and
  EACCESes on non-empty dirs).

## Token expiry (decision forced here)

A computer-less device with the GitHub App's default 8-hour expiring token
must store the refresh token and handle refresh — including
refresh-fails-while-offline, a whole failure mode. **Turn token expiry OFF in
the app settings** (the open item in the app setup) — with expiry off, the
device-flow token behaves like the fine-grained PAT it replaces.

## What the bench runs pinned down

Three constraints the on-device clone runs left behind. Each one is a fix that
looks removable and is not:

- **The clone worker is spawned at the top of the wizard, before any radio
  work.** A FreeRTOS stack comes from internal DRAM, and by the clone step
  Wi-Fi plus the sign-in TLS have fragmented that pool below a contiguous
  96 KB — the spawn fails `os error 12` with total capacity still fine. The
  worker parks on a channel and runs the clone when the step sends the job
  (the git service grabs its stack at boot for the same reason).
- **`clone_repo` installs the embedded GitHub CA bundle itself.** In normal
  operation that happens in the git service's `ensure_online`, which the wizard
  runs *before*; without it libgit2's mbedTLS stream rejects github.com
  `NOT_TRUSTED (0x08)` even though the device-flow POSTs to the same host
  validate (those use esp-idf's own bundle).
- **The origin step is idempotent** (reuse/repoint). A failed attempt leaves
  `/sd/repo` init'd with `origin` set, and a plain add dies at
  `remote 'origin' already exists` on the retry.

Two deviations from the plan above, both deliberate:

- **Default seeding is skipped** at clone: the editor falls back to built-in
  defaults and the repo carries its own `.typoena.toml` / snippets. Canonical
  firmware-side defaults remain future work.
- **The dirty guard reads only the `.typoena-dirty` journal**, never libgit2
  stranded-commit state — a failed `:gs` returns its paths to the journal, so a
  stranded commit already shows as a non-empty journal, and opening the repo
  with libgit2 on the wizard's stack isn't worth the cost.

## Non-goals

- SoftAP / captive portal / any embedded web UI.
- Creating GitHub repos from the device.
- Cloning large repos on-device (the gate refuses; the installer or a manual
  card seed covers them).
- Partial-clone proxy infrastructure (parked).
