typoena/typewriter/firmware/src/infrastructure/wizard_io.rs

//! Firmware driver for the onboarding wizard (v0.9 slices 2–3).
//!
//! The wizard crate is pure logic; this module is its I/O: keys from
//! `usb_kbd`, frames to the panel, and the effects executed against real
//! hardware. Runs *before* the net thread spawns.
//!
//! Radio ownership: the Wi-Fi half of the modem is reborrowed once
//! (`split_reborrow`) and the `EspWifi` built from it is **kept up for the
//! whole wizard** — sign-in, repo listing and clone are all network steps.
//! Dropping it when `run` returns releases the modem for the net thread,
//! which re-associates on the first `:gs` (a session's second join is fast).
//!
//! HTTPS: `EspHttpConnection` over the esp-idf certificate bundle (the
//! Spike 6 stack — `CONFIG_MBEDTLS_CERTIFICATE_BUNDLE=y`), after an SNTP
//! sync (cert validity needs a sane wall clock). The GitHub device flow's
//! pure half (bodies, parsers) lives in `wizard::github`, host-tested.
//!
//! Slice status: Wi-Fi + device-flow sign-in (QR on panel, poll-to-token,
//! `GET /user` identity), the repo list (`FetchRepos`) and the shallow
//! `Clone` are all real. The clone runs on a worker thread spawned *before*
//! the radio comes up — its 96 KB stack needs a contiguous internal-DRAM
//! block that Wi-Fi would otherwise fragment away (the git service dodges the
//! same trap by spawning at boot).

use std::sync::mpsc::{Receiver, TryRecvError};
use std::time::{Duration, Instant};

use anyhow::{anyhow, bail, Context, Result};
use embedded_svc::http::Method;
use esp_idf_svc::eventloop::EspSystemEventLoop;
use esp_idf_svc::hal::delay::FreeRtos;
use esp_idf_svc::hal::modem::{Modem, WifiModem};
use esp_idf_svc::http::client::{Configuration as HttpConfig, EspHttpConnection};
use esp_idf_svc::nvs::EspDefaultNvsPartition;
use esp_idf_svc::wifi::{BlockingWifi, ClientConfiguration, Configuration, EspWifi};

use display::{Frame, HEIGHT};
use wizard::github;
use wizard::{Effect, Event, RepoChoice, Wizard};

use crate::drivers::keyboard_usb as usb_kbd;
use crate::drivers::screen_epd::Epd;
use crate::drivers::wifi_esp::{connect_wifi, sync_clock};
use crate::infrastructure::storage_sd::Storage;

/// Progress from the background clone thread (see `Effect::Clone`), drained in
/// the main loop's idle branch and turned into wizard `Event`s.
enum CloneMsg {
    Progress(String),
    Done,
    Failed(String),
}

/// A clone job handed to the pre-spawned worker thread. Creds ride along
/// because `CARD_CONF` isn't set until the wizard returns.
struct CloneReq {
    remote_url: String,
    gh_user: String,
    token: String,
}

/// An in-flight device-flow grant the main loop polls between keystrokes.
struct PendingAuth {
    device_code: String,
    interval: Duration,
    next_poll: Instant,
    deadline: Instant,
}

/// Run the wizard to completion and return the final conf for the normal
/// boot path to install (`set_card_conf`). Blocks the boot; the editor only
/// exists after this returns. An `Err` is terminal (main `boot_halt`s with
/// it) — today that includes reaching the not-yet-built repo step.
///
/// NOTE: this code is compiled at `opt-level = 2`, not the workspace-wide `"s"`
/// — see the `[profile.release.package.firmware]` block in Cargo.toml. `run` is
/// an enormous function, and at `"s"` the Xtensa backend miscompiled it: spilled
/// argument slots and by-value struct copies were left reading `0xa5a5a5a5`
/// (FreeRTOS stack-fill), a LoadProhibited boot loop on every card entering the
/// wizard. The fault relocated with every codegen change (arg order/count,
/// inline hints, by-ref vs by-value) but never cleared at `"s"`; the opt-level
/// override is what fixes it. The signature is still kept lean — `start` by
/// reference, the radio singletons owned only briefly in `build_radio` — which
/// is good practice regardless, but it is not what makes the crash go away.
pub fn run(
    epd: &mut Epd,
    storage: &Storage,
    start: &conf::Conf,
    setup: bool,
    sys_loop: &EspSystemEventLoop,
    nvs: &EspDefaultNvsPartition,
    modem: &mut Modem,
) -> Result<conf::Conf> {
    // `:setup` opens the reset menu prefilled from the card conf; first boot /
    // power-pull resume walks the steps linearly from the first unmet one. The
    // dirty flag (unpushed-work journal) only sharpens the factory-reset
    // warning, so it's read once at construction.
    let mut wiz = if setup {
        Wizard::setup(start.clone(), storage.has_dirty())
    } else if *start == conf::Conf::default() && !storage.repo_present() {
        // A blank/foreign card the person brought — nothing Typoena on it. Gate
        // on consent before we touch it; accepting wipes it and dedicates it.
        // A power-pull mid-onboarding writes conf fields, so a resume no longer
        // matches this and skips the gate (falls to `resume` below).
        Wizard::adopt_blank_card()
    } else {
        Wizard::resume(start.clone())
    };
    let mut frame = Frame::new_white();
    let mut queue: Vec<Effect> = wiz.pending().into_iter().collect();
    let mut first_paint = true;
    let mut dirty = true;

    // Radio state for the whole run (see module docs). Built lazily, the first
    // time an effect needs Wi-Fi (below), from the owned `sys_loop`/`nvs` +
    // reborrowed modem — never from a threaded reference (see run's doc comment
    // / `build_radio`).
    let (wifi_modem, _) = modem.split_reborrow();
    let mut wifi_modem = Some(wifi_modem);
    let mut wifi: Option<BlockingWifi<EspWifi<'_>>> = None;
    let mut clock_synced = false;
    let mut pending_auth: Option<PendingAuth> = None;

    // Clone runs on a dedicated 96 KB thread (libgit2's path-buffer nesting
    // overflows the main task stack). Spawn it *now*, before any Wi-Fi work:
    // FreeRTOS stacks come from internal DRAM, and once the radio is up that
    // pool is too fragmented for a 96 KB contiguous block — the very failure
    // the git service sidesteps by grabbing its stack at boot. The worker
    // parks on `clone_req_rx` until the clone step sends a job (`clone_tx`),
    // and exits when that sender drops as `run` returns. Progress/outcome come
    // back on `clone_msg_rx`, drained in the idle branch.
    let (clone_tx, clone_req_rx) = std::sync::mpsc::channel::<CloneReq>();
    let (clone_msg_tx, clone_msg_rx) = std::sync::mpsc::channel::<CloneMsg>();
    std::thread::Builder::new()
        .name("wizclone".into())
        .stack_size(crate::infrastructure::net::GIT_STACK)
        .spawn(move || clone_worker(clone_req_rx, clone_msg_tx))
        .context("spawning the clone worker")?;
    let (int_free, int_largest) = unsafe {
        use esp_idf_svc::sys::{heap_caps_get_free_size, heap_caps_get_largest_free_block, MALLOC_CAP_INTERNAL};
        (
            heap_caps_get_free_size(MALLOC_CAP_INTERNAL),
            heap_caps_get_largest_free_block(MALLOC_CAP_INTERNAL),
        )
    };
    log::info!(
        "wizard: clone worker up ({} KB stack); internal DRAM free {} B (largest block {} B)",
        crate::infrastructure::net::GIT_STACK / 1024,
        int_free,
        int_largest,
    );

    loop {
        // Paint before executing: waiting screens ("Joining Wi-Fi…",
        // "contacting github.com…") must be visible while their effect blocks
        // below. First paint is a full refresh (clears the splash cleanly),
        // the rest ride the ~630 ms area partial like live typing does.
        if dirty {
            wiz.draw_into(&mut frame);
            if first_paint {
                epd.display_frame(frame.bytes())?;
                first_paint = false;
            } else {
                epd.display_frame_partial_window(frame.bytes(), 0, HEIGHT)?;
            }
            dirty = false;
        }

        if !queue.is_empty() {
            let fx = queue.remove(0);
            // Bring the radio up on demand, the first time an effect needs it.
            // Done here — not lazily inside the handlers — so `build_radio` is
            // fed the owned `sys_loop`/`nvs` locals directly (moved by value),
            // and no singleton *reference* is threaded through the handler call
            // chain. That threading is what the Xtensa codegen defect in run's
            // doc comment mishandles.
            if wifi.is_none()
                && matches!(
                    fx,
                    Effect::ScanWifi | Effect::TestWifi { .. } | Effect::StartAuth
                )
            {
                let m = wifi_modem
                    .take()
                    .context("radio unavailable (a previous Wi-Fi init failed)")?;
                wifi = Some(build_radio(m, sys_loop.clone(), nvs.clone())?);
            }
            match fx {
                Effect::WriteConf(c) => {
                    storage.write_conf(&c.render())?;
                    log::info!("wizard: conf persisted");
                }
                Effect::ScanWifi => {
                    let ev = match scan_wifi(wifi.as_mut().expect("radio built")) {
                        Ok(nets) => {
                            log::info!("wizard: scan found {} network(s)", nets.len());
                            Event::WifiScan(nets)
                        }
                        Err(e) => {
                            log::warn!("wizard: scan failed: {e:#}");
                            Event::WifiScanFailed(format!("{e:#}"))
                        }
                    };
                    queue.extend(wiz.event(ev));
                    dirty = true;
                }
                Effect::TestWifi { ssid, pass } => {
                    let ev = match join_wifi(wifi.as_mut().expect("radio built"), &ssid, &pass) {
                        Ok(()) => Event::WifiOk,
                        Err(e) => {
                            log::warn!("wizard: join failed: {e:#}");
                            Event::WifiFailed(format!("{e:#}"))
                        }
                    };
                    queue.extend(wiz.event(ev));
                    dirty = true;
                }
                Effect::StartAuth => {
                    pending_auth = None;
                    let ev =
                        match start_auth(wifi.as_mut().expect("radio built"), &mut clock_synced, wiz.conf()) {
                        Ok(dc) => {
                            log::info!(
                                "wizard: device flow started — code {} (expires in {}s)",
                                dc.user_code,
                                dc.expires_in_secs
                            );
                            let now = Instant::now();
                            let interval = Duration::from_secs(dc.interval_secs);
                            pending_auth = Some(PendingAuth {
                                device_code: dc.device_code,
                                interval,
                                next_poll: now + interval,
                                deadline: now + Duration::from_secs(dc.expires_in_secs),
                            });
                            Event::AuthCode {
                                verification_uri: dc.verification_uri,
                                user_code: dc.user_code,
                            }
                        }
                        Err(e) => {
                            log::warn!("wizard: device flow start failed: {e:#}");
                            Event::AuthFailed(format!("{e:#}"))
                        }
                    };
                    queue.extend(wiz.event(ev));
                    dirty = true;
                }
                Effect::FetchRepos => {
                    let token = wiz.conf().token.clone();
                    let ev = match fetch_repos(&token) {
                        Ok(repos) => {
                            log::info!("wizard: {} repo(s) available", repos.len());
                            Event::Repos(repos)
                        }
                        Err(e) => {
                            log::warn!("wizard: repo list failed: {e:#}");
                            Event::ReposFailed(format!("{e:#}"))
                        }
                    };
                    queue.extend(wiz.event(ev));
                    dirty = true;
                }
                Effect::Clone { full_name } => {
                    // Hand the job to the worker pre-spawned in `run` (see the
                    // spawn above) — it clones over the network the wizard
                    // already brought up. Progress/outcome come back on
                    // `clone_msg_rx`, drained in the idle branch.
                    let req = CloneReq {
                        remote_url: wiz.conf().remote_url.clone(),
                        gh_user: wiz.conf().gh_user.clone(),
                        token: wiz.conf().token.clone(),
                    };
                    log::info!("wizard: cloning {full_name} from {}", req.remote_url);
                    if clone_tx.send(req).is_err() {
                        queue.extend(
                            wiz.event(Event::CloneFailed("clone worker is gone".into())),
                        );
                        dirty = true;
                    }
                }
                Effect::DeleteRepo => {
                    // Repo switch (slice 5c): erase the current /sd/repo before
                    // the new clone. Runs here on the main task — the clone
                    // worker can't reach the !Send Storage. Blocks minutes on
                    // FAT; the "removing the old repo" line is already on the
                    // panel (painted before this effect ran). On failure, drop
                    // the queued WriteConf + Clone and report it: the wizard
                    // falls back to the pick list with disk truth cleared.
                    log::info!("wizard: repo switch — removing the old /sd/repo");
                    match storage.wipe_repo() {
                        Ok(()) => log::info!("wizard: old repo removed"),
                        Err(e) => {
                            log::warn!("wizard: repo delete failed: {e:#}");
                            queue.clear();
                            queue.extend(wiz.event(Event::CloneFailed(format!(
                                "removing the old repo: {e:#}"
                            ))));
                            dirty = true;
                        }
                    }
                }
                Effect::FactoryReset => {
                    // Erase the card, then reboot into first boot. The repo
                    // delete is minutes on FAT, so paint each coarse stage —
                    // the panel isn't frozen silently. Safe across a power-pull
                    // mid-wipe: the repo goes first and the conf last, so the
                    // next boot still reads unconfigured and re-enters here.
                    log::info!("wizard: factory reset — erasing the card");
                    let result = {
                        let mut paint = |line: &str| {
                            wiz.set_wiping(line);
                            wiz.draw_into(&mut frame);
                            let _ = epd.display_frame_partial_window(frame.bytes(), 0, HEIGHT);
                        };
                        storage.factory_reset(&mut paint)
                    };
                    match result {
                        Ok(()) => {
                            log::info!("wizard: factory reset complete — rebooting");
                            unsafe { esp_idf_svc::sys::esp_restart() };
                        }
                        Err(e) => {
                            log::warn!("wizard: factory reset failed: {e:#}");
                            queue.extend(wiz.event(Event::WipeFailed(format!("{e:#}"))));
                            dirty = true;
                        }
                    }
                }
                Effect::WipeCard => {
                    // Dedicate the card: erase every file on it, then walk into
                    // Wi-Fi (WipeCardDone) — unlike FactoryReset, no reboot. The
                    // Wiping screen is already painted (the consent Enter set it);
                    // wipe_card repaints its one progress line through `paint`.
                    log::info!("wizard: dedicate — erasing the whole card");
                    let result = {
                        let mut paint = |line: &str| {
                            wiz.set_wiping(line);
                            wiz.draw_into(&mut frame);
                            let _ = epd.display_frame_partial_window(frame.bytes(), 0, HEIGHT);
                        };
                        storage.wipe_card(&mut paint)
                    };
                    match result {
                        Ok(()) => {
                            log::info!("wizard: card erased — dedicated to Typoena");
                            queue.extend(wiz.event(Event::WipeCardDone));
                        }
                        Err(e) => {
                            log::warn!("wizard: card wipe failed: {e:#}");
                            queue.extend(wiz.event(Event::WipeFailed(format!("{e:#}"))));
                        }
                    }
                    dirty = true;
                }
                Effect::Decline => {
                    // Consent declined. Leave the card untouched and stop: main()
                    // boot_halts on this Err (idle with a message, no reboot loop).
                    log::info!("wizard: setup declined — card left untouched");
                    bail!(
                        "You chose not to set this card up for Typoena.\n\
                         Power off and insert your Typoena card."
                    );
                }
                Effect::Finish => return Ok(wiz.conf().clone()),
            }
            continue;
        }

        match usb_kbd::next_key() {
            Some(k) => {
                queue.extend(wiz.key(k));
                // Coalesce a typing burst into one repaint (and preserve any
                // effects each key produced, in order).
                while let Some(k) = usb_kbd::next_key() {
                    queue.extend(wiz.key(k));
                }
                dirty = true;
            }
            None => {
                // Idle: drain the clone worker's progress/outcome. Empty until
                // the clone step sends a job; the worker parks otherwise.
                match clone_msg_rx.try_recv() {
                    Ok(CloneMsg::Progress(s)) => {
                        queue.extend(wiz.event(Event::CloneProgress(s)));
                        dirty = true;
                        continue;
                    }
                    Ok(CloneMsg::Done) => {
                        queue.extend(wiz.event(Event::CloneDone));
                        dirty = true;
                        continue;
                    }
                    Ok(CloneMsg::Failed(e)) => {
                        queue.extend(wiz.event(Event::CloneFailed(e)));
                        dirty = true;
                        continue;
                    }
                    Err(TryRecvError::Empty) => {}
                    Err(TryRecvError::Disconnected) => {
                        // Worker thread died (e.g. clone stack overflow).
                        queue.extend(wiz.event(Event::CloneFailed(
                            "clone thread ended unexpectedly".into(),
                        )));
                        dirty = true;
                        continue;
                    }
                }

                // Advance an in-flight sign-in at GitHub's pace.
                if let Some(pa) = pending_auth.as_mut() {
                    let now = Instant::now();
                    if now >= pa.deadline {
                        pending_auth = None;
                        queue.extend(wiz.event(Event::AuthFailed(
                            "the code expired - retry for a fresh one".into(),
                        )));
                        dirty = true;
                        continue;
                    }
                    if now >= pa.next_poll {
                        match poll_token(&pa.device_code) {
                            Ok(github::Poll::Token(token)) => {
                                pending_auth = None;
                                let ev = match fetch_identity(&token) {
                                    Ok((login, name, email)) => Event::AuthDone {
                                        token,
                                        login,
                                        name,
                                        email,
                                    },
                                    Err(e) => {
                                        log::warn!("wizard: /user failed: {e:#}");
                                        Event::AuthFailed(format!("{e:#}"))
                                    }
                                };
                                queue.extend(wiz.event(ev));
                                dirty = true;
                            }
                            Ok(github::Poll::Pending) => pa.next_poll = now + pa.interval,
                            Ok(github::Poll::SlowDown(secs)) => {
                                pa.interval = Duration::from_secs(secs);
                                pa.next_poll = now + pa.interval;
                            }
                            Ok(github::Poll::Failed(reason)) => {
                                pending_auth = None;
                                queue.extend(wiz.event(Event::AuthFailed(reason)));
                                dirty = true;
                            }
                            Err(e) => {
                                // Transport hiccup — keep polling until the
                                // code's own deadline says otherwise.
                                log::warn!("wizard: poll failed (will retry): {e:#}");
                                pa.next_poll = now + pa.interval;
                            }
                        }
                        continue;
                    }
                }
                FreeRtos::delay_ms(10);
            }
        }
    }
}

/// The pre-spawned clone thread (see the spawn in `run`): parks on `req_rx`,
/// runs one shallow clone per job against the wizard's live Wi-Fi — it never
/// touches the modem, the main task owns the radio — and streams
/// progress/outcome back on `msg_tx`. Exits when the request sender drops (the
/// wizard finished). Its 96 KB stack is grabbed at spawn time, before Wi-Fi
/// fragments internal DRAM, which is the whole point of spawning it early.
fn clone_worker(req_rx: Receiver<CloneReq>, msg_tx: std::sync::mpsc::Sender<CloneMsg>) {
    for req in req_rx {
        let ptx = msg_tx.clone();
        let progress = move |phase: app::Phase| {
            let _ = ptx.send(CloneMsg::Progress(phase.label()));
        };
        let msg = match crate::infrastructure::net::clone_repo(
            &req.remote_url,
            &req.gh_user,
            &req.token,
            &progress,
        ) {
            Ok(n) => {
                log::info!("wizard: clone wrote {n} file(s)");
                CloneMsg::Done
            }
            Err(e) => {
                log::warn!("wizard: clone failed: {e:#}");
                CloneMsg::Failed(format!("{e:#}"))
            }
        };
        let _ = msg_tx.send(msg);
    }
}

/// Build the persistent radio once, in its own non-inlined frame with the
/// event-loop / NVS singletons **owned** rather than threaded down as
/// references — the shape that dodges the Xtensa spilled-reference crash (see
/// `run`'s doc comment; this mirrors the flat `wifi_tls` spike). `EspWifi` keeps
/// its own `Arc` clones of both, so the originals are free to drop on return.
#[inline(never)]
fn build_radio<'d>(
    modem: WifiModem<'d>,
    sys_loop: EspSystemEventLoop,
    nvs: EspDefaultNvsPartition,
) -> Result<BlockingWifi<EspWifi<'d>>> {
    // Internal DRAM at the moment Wi-Fi comes up. esp_wifi_init needs a
    // contiguous internal (DMA-capable) block; the 96 KB clone worker already
    // holds one, so this is where a starved pool would bite (see the
    // SPIRAM_TRY_ALLOCATE_WIFI_LWIP note in sdkconfig.defaults).
    let (int_free, int_largest) = unsafe {
        use esp_idf_svc::sys::{
            heap_caps_get_free_size, heap_caps_get_largest_free_block, MALLOC_CAP_INTERNAL,
        };
        (
            heap_caps_get_free_size(MALLOC_CAP_INTERNAL),
            heap_caps_get_largest_free_block(MALLOC_CAP_INTERNAL),
        )
    };
    log::info!(
        "wizard: bringing up the Wi-Fi radio — internal DRAM free {int_free} B (largest block {int_largest} B)"
    );
    let esp_wifi = EspWifi::new(modem, sys_loop.clone(), Some(nvs))?;
    Ok(BlockingWifi::wrap(esp_wifi, sys_loop)?)
}

/// Scan for nearby networks so the SSID can be picked, not typed. Leaves the
/// radio built-but-stopped so the join path's `start()` runs from a clean
/// state. Returns SSIDs deduped and strongest-first, hidden (blank) ones
/// dropped.
fn scan_wifi<'d>(w: &mut BlockingWifi<EspWifi<'d>>) -> Result<Vec<String>> {
    // Scanning needs the radio started in station mode; a default client
    // config is enough — we read beacons, never associate here.
    w.set_configuration(&Configuration::Client(ClientConfiguration::default()))?;
    w.start()?;
    let aps = w.scan().context("Wi-Fi scan failed")?;
    let _ = w.stop();

    // Dedup by SSID (mesh APs repeat the name), keep the strongest signal,
    // drop hidden networks (blank SSID), then sort strongest-first.
    let mut best: Vec<(String, i8)> = Vec::new();
    for ap in aps {
        let ssid = ap.ssid.as_str().to_string();
        if ssid.is_empty() {
            continue;
        }
        match best.iter_mut().find(|(s, _)| *s == ssid) {
            Some((_, rssi)) => *rssi = (*rssi).max(ap.signal_strength),
            None => best.push((ssid, ap.signal_strength)),
        }
    }
    best.sort_by_key(|&(_, rssi)| std::cmp::Reverse(rssi));
    Ok(best.into_iter().map(|(s, _)| s).collect())
}

/// (Re)associate the already-built radio with the given credentials. The
/// `EspWifi` persists across calls; only the association changes.
fn join_wifi<'d>(w: &mut BlockingWifi<EspWifi<'d>>, ssid: &str, pass: &str) -> Result<()> {
    if w.is_connected().unwrap_or(false) {
        // Re-testing (new creds after a failure, or :setup later): start clean.
        let _ = w.disconnect();
    }
    connect_wifi(w, ssid, pass)?;
    let ip = w.wifi().sta_netif().get_ip_info()?;
    log::info!("wizard: joined {ssid}, ip {}", ip.ip);
    Ok(())
}

/// Network preamble + `POST login/device/code`. The Wi-Fi step normally ran
/// just before, but a resume can land here directly — (re)join with the conf's
/// credentials if not already associated, sync the clock once, then start the
/// flow.
fn start_auth<'d>(
    w: &mut BlockingWifi<EspWifi<'d>>,
    clock_synced: &mut bool,
    conf: &conf::Conf,
) -> Result<github::DeviceCode> {
    if !w.is_connected().unwrap_or(false) {
        join_wifi(w, &conf.wifi_ssid, &conf.wifi_pass).context("joining Wi-Fi")?;
    }
    if !*clock_synced {
        sync_clock().context("syncing the clock (TLS needs it)")?;
        *clock_synced = true;
    }
    let body = post_form(github::DEVICE_CODE_URL, &github::device_code_body())
        .context("asking GitHub for a device code")?;
    github::parse_device_code(&body).map_err(|e| anyhow!(e))
}

/// One `POST login/oauth/access_token` poll.
fn poll_token(device_code: &str) -> Result<github::Poll> {
    let body = post_form(github::TOKEN_URL, &github::poll_body(device_code))?;
    Ok(github::parse_poll(&body))
}

/// One authenticated GitHub API GET; returns the body, erroring on non-2xx.
/// The `api.github.com` replies (a repo list especially) dwarf the OAuth
/// bodies, hence the generous cap — the buffer lands on PSRAM.
fn github_get(token: &str, url: &str) -> Result<String> {
    let mut conn = https_conn()?;
    let auth = format!("Bearer {token}");
    let headers = [
        ("User-Agent", "typoena-device"),
        ("Accept", "application/vnd.github+json"),
        ("X-GitHub-Api-Version", "2022-11-28"),
        ("Authorization", auth.as_str()),
    ];
    conn.initiate_request(Method::Get, url, &headers)
        .with_context(|| format!("GET {url}"))?;
    conn.initiate_response()?;
    let status = conn.status();
    let body = read_body(&mut conn, 2 * 1024 * 1024)?;
    if !(200..300).contains(&status) {
        bail!("GitHub {url} answered {status}");
    }
    Ok(body)
}

/// `GET /user` → (login, name, email) for the commit identity.
fn fetch_identity(token: &str) -> Result<(String, String, String)> {
    let body = github_get(token, github::USER_URL).context("GET /user")?;
    github::parse_user(&body).map_err(|e| anyhow!(e))
}

/// The repos the app installation can reach, with sizes for the wizard's gate:
/// list the user's installations, then each one's repositories. Deduped across
/// installations, sorted by name. Empty list → the app isn't installed
/// anywhere yet (signing in proves identity, not repo access), so point at the
/// install page rather than showing a blank list.
fn fetch_repos(token: &str) -> Result<Vec<RepoChoice>> {
    let body = github_get(token, github::INSTALLATIONS_URL).context("listing installations")?;
    let ids = github::parse_installation_ids(&body).map_err(|e| anyhow!(e))?;
    if ids.is_empty() {
        bail!(
            "no GitHub App installation - install Typoena on the repo you want first: {}",
            github::APP_INSTALL_URL
        );
    }
    let mut out: Vec<RepoChoice> = Vec::new();
    for id in ids {
        let body = github_get(token, &github::installation_repos_url(id))
            .with_context(|| format!("listing repos for installation {id}"))?;
        for (full_name, size_kb) in github::parse_repos(&body).map_err(|e| anyhow!(e))? {
            if !out.iter().any(|r| r.full_name == full_name) {
                out.push(RepoChoice { full_name, size_kb });
            }
        }
    }
    out.sort_by_key(|r| r.full_name.to_lowercase());
    Ok(out)
}

/// One TLS connection against the esp-idf certificate bundle (Spike 6).
fn https_conn() -> Result<EspHttpConnection> {
    EspHttpConnection::new(&HttpConfig {
        crt_bundle_attach: Some(esp_idf_svc::sys::esp_crt_bundle_attach),
        ..Default::default()
    })
    .context("creating the HTTPS connection (TLS init)")
}

/// Form-encoded POST; returns the body regardless of status — GitHub's OAuth
/// endpoints put errors in parseable `error=` fields, sometimes on a 4xx.
fn post_form(url: &str, body: &str) -> Result<String> {
    let mut conn = https_conn()?;
    let len = body.len().to_string();
    let headers = [
        ("User-Agent", "typoena-device"),
        ("Content-Type", "application/x-www-form-urlencoded"),
        ("Content-Length", len.as_str()),
    ];
    conn.initiate_request(Method::Post, url, &headers)
        .with_context(|| format!("POST {url}"))?;
    conn.write_all(body.as_bytes()).context("sending the form")?;
    conn.initiate_response()?;
    let status = conn.status();
    let reply = read_body(&mut conn, 16 * 1024)?;
    log::info!("wizard: POST {url} -> {status} ({} B)", reply.len());
    Ok(reply)
}

/// Drain a response into a String; `max` guards against reading something
/// unexpected forever (OAuth replies are a few hundred bytes, an API repo
/// list can be a few hundred KB).
fn read_body(conn: &mut EspHttpConnection, max: usize) -> Result<String> {
    let mut out = Vec::new();
    let mut buf = [0u8; 2048];
    loop {
        let n = conn.read(&mut buf)?;
        if n == 0 {
            break;
        }
        out.extend_from_slice(buf.get(..n).unwrap_or_default());
        if out.len() > max {
            bail!("reply unexpectedly large (> {} KB)", max / 1024);
        }
    }
    Ok(String::from_utf8_lossy(&out).into_owned())
}
