typoena/typewriter/installer/src/app.rs

//! Wizard state: which step we're on, the results each step produces, and
//! step-aware key handling (nav steps, the Configure form, and the SD-card step
//! each behave differently).

use std::sync::Arc;
use std::sync::atomic::{AtomicBool, Ordering};
use std::sync::mpsc::{Receiver, TryRecvError};
use std::time::Instant;

use ratatui::crossterm::event::{KeyCode, KeyEvent, KeyModifiers};

use crate::auth::{self, AuthEvent};
use crate::config::{Config, Field, keychain_wifi_password};
use crate::preflight::Preflight;
use crate::sdcard::{self, Card, CardInspect, SdEvent};

#[derive(Clone, Copy, PartialEq, Eq)]
pub enum Step {
    Preflight,
    Configure,
    SdCard,
    Done,
}

impl Step {
    pub const ALL: [Step; 4] = [Step::Preflight, Step::Configure, Step::SdCard, Step::Done];

    pub fn title(self) -> &'static str {
        match self {
            Step::Preflight => "Preflight",
            Step::Configure => "Configure",
            Step::SdCard => "SD card",
            Step::Done => "Done",
        }
    }

    pub fn index(self) -> usize {
        Step::ALL.iter().position(|&s| s == self).unwrap_or(0)
    }

    fn next(self) -> Step {
        Step::ALL.get(self.index() + 1).copied().unwrap_or(self)
    }

    fn prev(self) -> Step {
        Step::ALL.get(self.index().saturating_sub(1)).copied().unwrap_or(self)
    }
}

/// The "Sign in with GitHub" device flow (started with ^G on Configure). While
/// it's not Idle the Configure step is modal: the sign-in panel owns the keys
/// (Esc cancels, o reopens the browser) so the user can't half-edit the form
/// while a background worker is about to overwrite the token field.
pub enum AuthState {
    Idle,
    /// Asking GitHub for a one-time code.
    Starting,
    /// Code issued — the user is off authorizing in the browser; we poll.
    Waiting {
        user_code: String,
        verification_uri: String,
    },
}

/// The proactive repo-access probe (does the token see the notes repo?). Each
/// verdict remembers which remote it judged, so editing the field silently
/// retires a stale flag instead of mislabeling the new URL.
pub enum RepoCheck {
    NotRun,
    Checking { remote: String },
    Granted { remote: String },
    Missing { remote: String },
}

pub enum SdState {
    Idle,
    /// The selected card already holds a repo; awaiting an explicit `y` to wipe.
    ConfirmWipe(CardInspect),
    Running,
    Done,
    Failed(String),
}

/// A background computation currently owning the UI. Each variant carries the
/// caption shown next to the spinner while the work runs off the UI thread; the
/// point is that a shell-out (diskutil, git, the Keychain prompt) never freezes
/// the render loop mid-wizard.
#[derive(Clone, Copy, PartialEq, Eq)]
pub enum Busy {
    None,
    Preflight,
    DetectingCards,
    PreparingCard,
    Keychain,
}

impl Busy {
    /// Spinner caption, or None when idle.
    pub fn label(self) -> Option<&'static str> {
        match self {
            Busy::None => None,
            Busy::Preflight => Some("Checking your Mac…"),
            Busy::DetectingCards => Some("Scanning for SD cards…"),
            Busy::PreparingCard => Some("Reading the card…"),
            Busy::Keychain => Some("Asking Keychain…"),
        }
    }
}

/// The output of a background task, applied on the UI thread when it lands.
enum TaskResult {
    Preflight(Preflight),
    Cards(Vec<Card>),
    Prepared {
        has_repo: bool,
        inspect: Option<CardInspect>,
    },
    Keychain {
        ssid: String,
        pw: Option<String>,
    },
}

pub struct App {
    pub step: Step,
    pub preflight: Preflight,
    pub config: Config,
    /// Focused field index within the Configure form.
    pub focus: usize,
    /// Transient one-line feedback (e.g. the Keychain-lookup result).
    pub status: Option<String>,
    // ── SD-card step ──
    pub cards: Vec<Card>,
    pub card_sel: usize,
    pub sd: SdState,
    pub sd_log: Vec<String>,
    /// Latest git-progress tick (phase, 0..=100), driving the SD-step gauge.
    pub sd_progress: Option<(String, u16)>,
    sd_rx: Option<Receiver<SdEvent>>,
    // ── GitHub sign-in (device flow) ──
    pub auth: AuthState,
    auth_rx: Option<Receiver<AuthEvent>>,
    /// Raised to stop the polling worker when the user cancels.
    auth_cancel: Option<Arc<AtomicBool>>,
    /// Proactive "can this token see the repo" probe (advisory — never blocks).
    pub repo_check: RepoCheck,
    check_rx: Option<Receiver<(String, auth::RepoAccess)>>,
    // ── background computation ──
    /// The off-thread work currently running (spinner + locked input), if any.
    pub busy: Busy,
    /// Frame counter, bumped once per render loop, animating the spinner.
    pub tick: u64,
    /// When the UI came up — the wall-clock origin the header's typewriter
    /// intro plays against, so its pace is independent of the render cadence.
    pub started: Instant,
    task_rx: Option<Receiver<TaskResult>>,
    pub should_quit: bool,
}

impl App {
    pub fn new() -> Self {
        App {
            step: Step::Preflight,
            // Filled by the startup task (see `begin_startup`) so launch paints
            // immediately instead of blocking on the diskutil scan.
            preflight: Preflight { checks: Vec::new() },
            config: Config::derived(),
            focus: 0,
            status: None,
            cards: Vec::new(),
            card_sel: 0,
            sd: SdState::Idle,
            sd_log: Vec::new(),
            sd_progress: None,
            sd_rx: None,
            auth: AuthState::Idle,
            auth_rx: None,
            auth_cancel: None,
            repo_check: RepoCheck::NotRun,
            check_rx: None,
            busy: Busy::Preflight,
            tick: 0,
            started: Instant::now(),
            task_rx: None,
            should_quit: false,
        }
    }

    /// Kick the first environment scan off the UI thread. Call once, right after
    /// construction — `new()` leaves `busy = Preflight` so the first frame already
    /// shows the spinner. (Kept out of `new()` so tests stay thread-free.)
    pub fn begin_startup(&mut self) {
        self.begin_preflight();
    }

    pub fn on_key(&mut self, key: KeyEvent) {
        // Ctrl-C always quits, on any step (even mid-typing / mid-run).
        if key.modifiers.contains(KeyModifiers::CONTROL) && key.code == KeyCode::Char('c') {
            self.should_quit = true;
            return;
        }
        // A background computation owns the UI — ignore input until it lands
        // (Ctrl-C above is the one escape). Tasks are short shell-outs.
        if self.busy != Busy::None {
            return;
        }
        self.status = None;
        // Ctrl-N / Ctrl-P jump a whole step from anywhere, independent of the
        // in-step field/card focus (Tab only spills at the ends). Back is always
        // safe; forward respects the same gate as the per-step forward keys — so
        // on the SD step (forward is earned by writing the card) ^N refuses and
        // says why via the status snackbar. Suppressed while the SD step owns a
        // modal (a running write, or the wipe-confirm), where leaving is wrong —
        // those keys fall through to the SD handler, which ignores them.
        let sd_modal = self.step == Step::SdCard
            && matches!(self.sd, SdState::Running | SdState::ConfirmWipe(_));
        // The GitHub sign-in panel is modal the same way: leaving Configure
        // mid-flow would strand the code screen, so ^N/^P fall through to the
        // Configure handler, which routes them to the panel's own keys.
        let auth_modal = self.step == Step::Configure && !matches!(self.auth, AuthState::Idle);
        if !sd_modal && !auth_modal && key.modifiers.contains(KeyModifiers::CONTROL) {
            match key.code {
                KeyCode::Char('p') => {
                    self.prev();
                    return;
                }
                KeyCode::Char('n') => {
                    match self.step {
                        Step::SdCard => {
                            self.status =
                                Some("write the card to finish this step — ^P steps back".into());
                        }
                        Step::Done => {}
                        _ => self.next(),
                    }
                    return;
                }
                _ => {}
            }
        }
        match self.step {
            Step::Configure => self.on_key_configure(key),
            Step::SdCard => self.on_key_sdcard(key),
            _ => self.on_key_nav(key),
        }
    }

    /// Non-form steps: single-key navigation. Arrows, Tab/Shift-Tab, and vim
    /// h/j/k/l all move between steps so no pointer or arrow key is required.
    fn on_key_nav(&mut self, key: KeyEvent) {
        match key.code {
            KeyCode::Char('q') | KeyCode::Esc => self.should_quit = true,
            KeyCode::Char('r') if self.step == Step::Preflight => self.begin_preflight(),
            KeyCode::Enter
            | KeyCode::Tab
            | KeyCode::Down
            | KeyCode::Right
            | KeyCode::Char('j')
            | KeyCode::Char('l') => self.next(),
            KeyCode::Up
            | KeyCode::BackTab
            | KeyCode::Left
            | KeyCode::Char('k')
            | KeyCode::Char('h') => self.prev(),
            _ => {}
        }
    }

    /// Configure form: typing edits the focused field; field navigation spills
    /// over into step navigation at the ends.
    fn on_key_configure(&mut self, key: KeyEvent) {
        // The sign-in panel owns the keys while the device flow runs. Modified
        // chars (^N/^P step jumps land here too) are deliberately inert — only
        // a plain Esc/n/q cancels, so a reflexive ^N can't kill the flow.
        if !matches!(self.auth, AuthState::Idle) {
            match key.code {
                _ if key.modifiers != KeyModifiers::NONE => {}
                KeyCode::Esc | KeyCode::Char('n') | KeyCode::Char('q') => self.cancel_device_flow(),
                KeyCode::Char('o') => {
                    if let AuthState::Waiting {
                        verification_uri, ..
                    } = &self.auth
                    {
                        auth::open_browser(verification_uri);
                    }
                }
                _ => {}
            }
            return;
        }
        let ctrl = key.modifiers.contains(KeyModifiers::CONTROL);
        let last = Field::ALL.len() - 1;
        match key.code {
            KeyCode::Esc => self.should_quit = true,
            // Shift-Tab / ↑ walk fields up; past the first, back a step.
            KeyCode::Up | KeyCode::BackTab => {
                if self.focus > 0 {
                    self.focus -= 1;
                } else {
                    self.prev();
                }
            }
            KeyCode::Down if self.focus < last => self.focus += 1,
            // Tab walks fields down; past the last, on to the next step — so a
            // pure Tab/Shift-Tab rhythm carries you through the whole wizard.
            KeyCode::Tab => {
                if self.focus < last {
                    self.focus += 1;
                } else {
                    self.next();
                }
            }
            KeyCode::Enter => {
                if self.focus < last {
                    self.focus += 1;
                } else {
                    self.next();
                }
            }
            KeyCode::Char('u') if ctrl => self.config.get_mut(self.focused_field()).clear(),
            KeyCode::Char('k') if ctrl => self.fill_wifi_from_keychain(),
            KeyCode::Char('g') if ctrl => self.begin_device_flow(),
            // ^O: open the app-install page and watch for access. (^I would be
            // the mnemonic but Ctrl-I *is* Tab on a terminal.)
            KeyCode::Char('o') if ctrl => self.install_app(),
            KeyCode::Backspace => {
                self.config.get_mut(self.focused_field()).pop();
            }
            KeyCode::Char(c) if !ctrl => self.config.get_mut(self.focused_field()).push(c),
            _ => {}
        }
    }

    /// SD-card step: pick a card, then start (or confirm-wipe-then-start) the
    /// provision.
    fn on_key_sdcard(&mut self, key: KeyEvent) {
        match self.sd {
            SdState::Running => return,
            SdState::ConfirmWipe(_) => {
                match key.code {
                    KeyCode::Char('y') | KeyCode::Char('Y') => self.start_provision(true),
                    KeyCode::Char('n') | KeyCode::Char('N') | KeyCode::Esc => {
                        self.sd = SdState::Idle
                    }
                    _ => {}
                }
                return;
            }
            _ => {}
        }
        match key.code {
            KeyCode::Char('q') | KeyCode::Esc => self.should_quit = true,
            // ↑/k/Shift-Tab walk the card list up; past the top, back a step.
            KeyCode::Up | KeyCode::BackTab | KeyCode::Char('k') => {
                if self.card_sel > 0 {
                    self.card_sel -= 1;
                } else {
                    self.prev();
                }
            }
            KeyCode::Down | KeyCode::Char('j') if self.card_sel + 1 < self.cards.len() => {
                self.card_sel += 1;
            }
            KeyCode::Tab if self.card_sel + 1 < self.cards.len() => self.card_sel += 1,
            // ←/h steps back; forward is deliberately gated behind writing a card.
            KeyCode::Left | KeyCode::Char('h') => self.prev(),
            KeyCode::Char('r') => {
                self.sd = SdState::Idle;
                self.sd_log.clear();
                self.sd_progress = None;
                self.begin_detect_cards();
            }
            KeyCode::Enter => self.attempt_provision(),
            _ => {}
        }
    }

    pub fn focused_field(&self) -> Field {
        // An over-large focus clamps to the last field.
        Field::ALL.get(self.focus).or(Field::ALL.last()).copied().unwrap_or(Field::WifiSsid)
    }

    /// Whether the current step's forward gate is satisfied, so Enter/Tab may
    /// advance. Drives the sidebar's "ready / finish this step" affordance.
    pub fn forward_open(&self) -> bool {
        match self.step {
            Step::Preflight => true,
            Step::Configure => self.config.missing_required().is_empty(),
            Step::SdCard => matches!(self.sd, SdState::Done),
            Step::Done => false,
        }
    }

    /// The step a forward move would land on, if any (None on the last step).
    pub fn next_step(&self) -> Option<Step> {
        (self.step != Step::Done).then(|| self.step.next())
    }

    fn fill_wifi_from_keychain(&mut self) {
        let ssid = self.config.wifi_ssid.clone();
        if ssid.trim().is_empty() {
            self.status = Some("set the Wi-Fi SSID first, then ^K".into());
            return;
        }
        // The `security` lookup pops a macOS auth dialog and blocks until it's
        // dismissed — run it off-thread so the wizard doesn't freeze behind it.
        self.spawn(Busy::Keychain, move || {
            let pw = keychain_wifi_password(&ssid);
            TaskResult::Keychain { ssid, pw }
        });
    }
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
